williamapardis/SAGE/electrical/SAGE/17-0001 SAGE DETECT/simulation/SimpleAmpCircuit.asc

C2: cap; 1.8nF
I1: current; PULSE(0 0.000050 0 0.002 0 0 0 5)
I2: current; 180µ
R2: res; 5.5k
R3: res; 1.65k
R4: res; 1k
U1: ADA4528-2
U2: ADA4528-2
V1: voltage; 2v
V2: voltage; 2v
Named nets: Output, 0, +V, in, -V
;dc I1 0 8m 0.01m
.tran 10m
