williamapardis/SAGE/electrical/SAGE/17-0001 SAGE DETECT/simulation/voltageFollower.asc

R1: res; 10k
R4: res; 10k
U1: ADA4528-2
U2: ADA4528-2
V1: voltage; 2v
V2: voltage; 2v
Named nets: Output, 0, +V, -V
;dc I1 0 8m 0.01m
.tran 10m
